MBS212/Drivers-Pico/Images/pico-enclosure.jpg

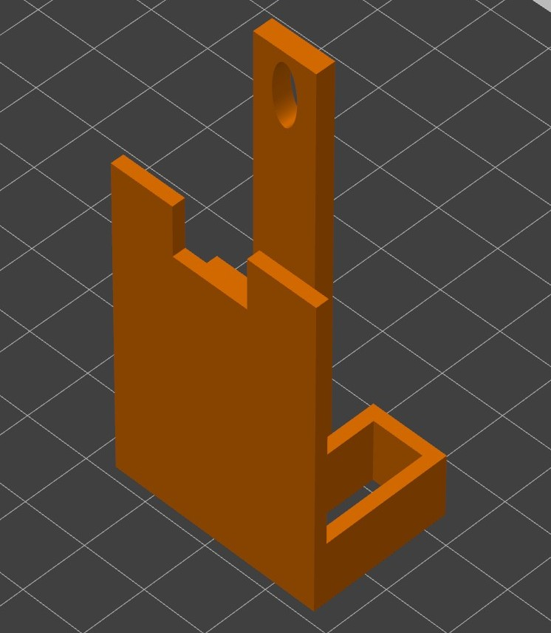
Images/pico-enclosure.jpg
